Ning0612/esp32-paper-frame/docs/adr/0005-weather-worker-and-status-bar.md

# ADR-0005：WeatherWorker HTTPS 契約與狀態列渲染基線

- Status: accepted
- Date: 2026-07-31
- Supersedes: none

## Context

`docs/archive/IMPLEMENTATION_PLAN.md` 的 Gate G7（"OpenWeatherMap endpoint/version、
TLS trust、cache schema 與 rate limit"）與狀態列 renderer 的字型/圖示來源
必須在 Phase 6 開工前固定，不能沿用草案「建議」直接實作。掃描確認：全專案
目前沒有任何 `esp_http_client`/`esp_tls`/`esp_crt_bundle` 用例、SNTP/mDNS
完全未整合、狀態列目前是整片填白（無文字/圖示繪製能力）。本 ADR 記錄
WeatherWorker（`pf_weather_worker` component）與狀態列渲染（`pf_display`
的 bitmap font/icon 原語）實作前必須固定的決策。

## Decision

### G7：OpenWeatherMap endpoint / TLS trust / cache schema / rate limit

- **Endpoint**：`GET https://api.openweathermap.org/data/2.5/weather`，
  查詢參數 `lat`、`lon`（由 `WeatherSettings.latitude_e6`/`longitude_e6`
  換算為十進位度）、`appid`、`units`、`lang`。對應既有
  `pf_weather::parse_current_weather` 已假設的回應欄位
  （`main.temp`、`main.humidity`、`weather[0].id/description/icon`、
  `dt`、`name`），不需要改動 parser 契約。
- **TLS trust**：使用 `esp_crt_bundle_attach`（`esp_http_client_config_t`
  的 `crt_bundle_attach` 欄位）。`sdkconfig.paperframe-s3` 已啟用
  `CONFIG_MBEDTLS_CERTIFICATE_BUNDLE=y` 與
  `CONFIG_MBEDTLS_CERTIFICATE_BUNDLE_DEFAULT_FULL=y`，不釘選、不內嵌自訂
  憑證。TLS 憑證有效期驗證需要正確的系統時間，因此 WeatherWorker 在首次
  請求前必須等待 `RuntimeSnapshot.time_sync == synced`（見下方 SNTP 決策）。
- **Cache schema**：直接複用既有 `pf_weather::Observation`/`Cache`
  （`components/pf_weather/include/pf_weather/weather.hpp`），不重新定義。
  `RuntimeSnapshot` 內嵌一份精簡欄位（`weather_observation`、
  `weather_units`、`weather_has_observation`、
  `weather_last_success_epoch_s`、`weather_consecutive_failures`、
  `weather_last_failure`），值語意複製，不使用指標，維持
  `RuntimeSnapshot` 的 trivially-copyable 契約。
- **Rate limit / 更新頻率**（**已被 [ADR-0014](0014-weather-panel-refresh-cadence-and-map-picker.md) 取代**）：
  改採 `WeatherSettings.update_interval_minutes`
  （使用者可設 10–1440 分鐘）取代 `pf_weather::kUpdateIntervalMs` 目前寫死
  的 10 分鐘；`pf_weather::record_success` 擴充一個 `interval_ms` 參數，
  預設值等於原常數以維持既有呼叫端相容。OpenWeatherMap 免費額度為
  60 requests/min，在 10–1440 分鐘區間內完全無虞，不需要額外的用戶端節流。

### SNTP：最小可用的時間同步

- NetworkServiceTask（既有 `pf_network::NetworkService`，
  `docs/archive/IMPLEMENTATION_PLAN.md` 第 60 行已將其列為 SNTP owner）在 STA
  首次取得 IP 後啟動 SNTP：`esp_netif_sntp_init` +
  `ESP_NETIF_SNTP_DEFAULT_CONFIG`，伺服器名稱來自
  `WeatherSettings.ntp_server`（預設 `pool.ntp.org`），透過
  `sntp_set_time_sync_notification_cb` 註冊回呼。
- 新增 `pf_network::TimeSyncState { unsynced, syncing, synced }`
  （純邏輯，`components/pf_network/include/pf_network/time_sync_state.hpp`）。
  刻意不設 `failed` 狀態：ESP-IDF 的 SNTP 客戶端沒有終止性失敗的概念，
  啟動後會持續在背景重試，沒有事件可以驅動這樣的狀態。
- `RuntimeSnapshot` 鏡射一份同名 `TimeSyncState`（避免 `pf_runtime`
  反向依賴 `pf_network`，沿用既有 `WifiState`/`InternetState` 的鏡射＋
  轉譯慣例），`RuntimeCoordinator::update_time_sync(...)` 是唯一寫入口。
- 本次只處理「STA 連上後啟動 SNTP、追蹤 synced 狀態」，不處理 AP/
  Recovery AP 模式下的時間行為，也不做未同步狀態的完整診斷分類；
  WeatherWorker 與狀態列渲染只需要一個布林等級的「時間是否可信」訊號。

### Internet 可達性訊號

- `NetworkStateMachine` 已定義 `internet_reachable`/`internet_unreachable`
  事件，但全專案沒有任何呼叫端觸發，導致 `internet` 狀態永遠停在
  `unknown`。WeatherWorker 是第一個會發出 HTTPS 請求的元件，因此由它
  透過 `NetworkService::report_internet_state(bool reachable)`
  （比照 `request_scan()` 的直接呼叫模式）回報：
  - `pf_weather::Cache::Failure::network`（DNS 解析、連線建立、TLS
    handshake 失敗）→ `unreachable`。
  - 其餘結果（成功、`api_key_invalid`、`http_error`、`parse_error`——
    皆代表已收到 HTTP 回應，代表連線本身是通的）→ `reachable`。
- 對應 `docs/archive/IMPLEMENTATION_PLAN.md` 第 203 行的既有原則：
  「DNS、weather 或 Internet 錯誤只改變 Internet 狀態，不進 AP」。

### 字型與圖示授權（**圖示部分已被 ADR-0013 取代**）

- 狀態列渲染（日期、星期、weather icon、temperature、stale 標記）採用
  **自製最小點陣字型**（僅涵蓋數字、`:`、`/`、`-`、`°`、`%`、星期縮寫
  所需的拉丁字母，本段落仍然有效）與 **9 組簡化天氣圖示分類**（對映
  OpenWeatherMap icon code 的天氣狀況群組）。天氣圖示原本的決策是「皆為
  本專案原創點陣資料，不引入任何第三方字型或圖示檔案，避免授權查證與
  再散布限制的負擔」——這個部分已被
  [ADR-0013](0013-weather-icon-bitmaps-from-third-party-ofl-source.md)
  取代：圖示改為轉檔自 `erikflowers/weather-icons`（OFL-1.1）的點陣圖，
  9 組分類本身不變。點陣字型（數字/日期）維持原創，不受影響。

## Consequences

- `pf_weather_worker` 是本專案第一個使用 `esp_http_client`/`esp-tls`/
  `mbedtls` 的 component；CMakeLists 需新增對應 `REQUIRES`。
- WeatherWorker 讀取設定一律呼叫 `pf_config::load_weather_settings()`
  直接讀 NVS，不與 `health_server.cpp` 內的 `server_access_config` 共用
  記憶體狀態，避免新增跨 component 耦合；使用者存檔後由
  `process_weather_config()` 呼叫 WeatherWorker 的
  `request_immediate_refresh()` 提前喚醒，不必等到下一個排程週期。
- 狀態列內容更新沿用既有整頁 refresh 節奏（不新增 `CommandKind`、不做
  局部刷新驅動）；天氣本身 10–1440 分鐘的更新頻率與既有 5–30 分鐘
  carousel refresh 週期已經匹配，此設計為刻意簡化，非遺漏
  （**更新頻率的排程來源本身已被 [ADR-0014](0014-weather-panel-refresh-cadence-and-map-picker.md)
  取代**：不再有獨立的使用者可調間隔，改為 carousel 每次面板刷新前
  觸發，但「沿用整頁 refresh 節奏、不做局部刷新」這個更上層的設計仍然
  成立）。
- 未來若要改變 endpoint、TLS 策略或字型/圖示來源，需要新的 superseding
  ADR，而不是直接修改程式碼繞過本決策。

## Verification

- `pio run` 與 `pio test -e native` 全綠是本 ADR 所涵蓋所有變更的最低
  驗證門檻；HTTPS/SNTP 的實際網路行為無法 host test，須在
  `docs/hardware/VALIDATION.md` 記錄實機驗證（API key invalid、
  DNS/TLS/timeout 各自診斷狀態、stale 顯示、未同步時間 fallback）。
- `esp_crt_bundle_attach` 驗證 `api.openweathermap.org` 憑證成功，是
  WeatherWorker 第一次成功抓取的前提條件，須在實機記錄。

## Update (2026-08)

反過度設計整併：`pf_weather_worker` component 已併入 `pf_weather`，
namespace 由 `pf_weather_worker` 改為 `pf_weather`（`WeatherWorker` 類別
本體與本 ADR 記錄的所有決策不變，純粹是元件邊界調整，不是 superseding
ADR 的範疇）。本文其餘內容提到的 `pf_weather_worker` 是撰寫當下的元件
名稱，保留作歷史紀錄。

## Update (2026-08-03)

狀態列版面依產品需求固定為：日期左側顯示
`YYYY-MM-DD-<英文星期縮寫>`（例如 `2026-08-03-Mon`），裝置 IPv4 位址置中。
環境感測器狀態為 `online` 且有有效 reading 時，OpenWeatherMap 天氣圖示與
室外溫度接在日期右側，最右側顯示室內溫度與溼度；感測器未啟用或沒有有效
reading 時，右側室內欄位改顯示天氣圖示與室外溫度。IP 由 `NetworkService` 發布至唯一的
`RuntimeSnapshot`，不由 renderer 直接查詢網路介面。480px 直向狀態列採
較小點陣字級以保留三區的獨立位置；`^` 是韌體內部的一位元組度數符號。

## Update (2026-08-21)

本段落取代前述「SNTP：最小可用的時間同步」一節裡「不處理未同步狀態的完整診斷分類」
之外的範圍限制：狀態列現在會換算成使用者設定的當地時間，不再固定顯示 UTC。

- `ConfigRecord.timezone`（`pf_config` schema，`char[kTimezoneCapacity]`）改變意義：
  schema v2 及以前存的是 IANA 區域名稱（如 `"Asia/Taipei"`），但全專案從未真的拿它換算
  時間；schema v3 起改存 UTC 偏移字串（`"+8"`、`"-5.5"`、`"+5.75"`），由
  `pf_config::parse_timezone_offset_minutes()` 解析成分鐘數，支援到 15 分鐘（0.25 小時）
  精度以涵蓋 Nepal（+5:45）、Chatham Islands（+12:45）等半/45 分鐘時區，範圍
  UTC-12〜UTC+14。這裡刻意不引入 IANA tzdata／DST 規則：ESP-IDF 沒有內建時區資料庫，
  韌體只承諾"使用者輸入的固定偏移"，不承諾"跟著地區行事曆自動調整 DST"。
- 這個偏移值透過 `RuntimeCoordinator::update_timezone_offset()` 鏡射進
  `RuntimeSnapshot.timezone_offset_minutes`（比照既有 `time_sync`/`internet` 的鏡射慣例）；
  `build_status_bar_content()`（`src/app_main.cpp`）在 `gmtime_r()` 之前把 SNTP 取得的
  UTC epoch 加上這個偏移，換算出的日期／星期即為當地時間。除了狀態列這一處，其餘
  epoch 用途（快取新鮮度、OTA 時間戳記）仍刻意維持 UTC，避免時區偏移污染以「距今
  多少秒」為準的比較邏輯。
- WebUI「天氣與時間」頁新增一個獨立的「時區」面板／表單（`data/web/index.html`
  `#timezone-form`），透過既有 `/api/v1/config`（`CarouselConfigForm` 新增可選的
  `timezone` 欄位）保存，與 `refresh_minutes`/`random` 共用同一筆 `ConfigRecord`，
  但各自獨立可省略。
- Schema 由 v2 bump 到 v3；pre-v3 記錄遷移時，`timezone` 一律重設為新預設值 `"+8"`
  （不嘗試把舊的 IANA 名稱轉換成偏移——這欄位過去從未生效，沒有需要保留的使用者狀態）。

## Update (2026-08-04)

本段取代 2026-08-03 段落中的狀態列群組定位方式。依產品 UI 調整，狀態列仍
固定為 40px 高，但天氣圖示改為 36×36px，垂直位置
固定保留上下各 2px。橫向點陣文字放大為 4 倍，直向優先使用 3 倍；若直向
同時顯示最長的日期、IPv4、天氣與室內資訊而寬度不足，才退回 2 倍，讓文字
在同一個 40px 高度內保持可讀。日期、天氣（圖示／室外溫度）、IP、
室內溫度／溼度現在以內容寬度排列，存在的群組之間使用相同的可用空白；
缺少天氣或室內 reading 時只移除對應群組，不改變其他資訊的等距分配。

## Update (2026-09-03)

本段取代 2026-08-03 段落中「環境感測器狀態為 `online` 且有有效 reading
時才顯示室內溫濕度」的條件。使用者回報：全刷間隔（預設 30 分鐘）遠長於
原本的過期門檻（5 分鐘），單次 DHT22 讀取失敗、進入重試退避時，剛好被
全刷抓到就會讓室內欄位整個消失一輪。修正比照既有的 `weather_available`／
`weather_stale` 模式，新增 `indoor_stale`：室內欄位現在只要「已有成功讀值
（`has_reading`）且 `SensorStatus` 為 `online` **或** `stale`」就顯示
（過期門檻同時放寬到 3600 秒，比照 `pf_weather` 的門檻），過期時在數值
後方加一個紅色 `*` 標記；其餘狀態（`disabled`／`not_detected`／
`probing`／`error`，以及尚未成功讀過任何一次的情況）一律整個隱藏
（判斷邏輯集中在 `pf_sensors::environment_display_decision()`，見
`components/pf_sensors/include/pf_sensors/environment_sensor.hpp`）。
`kEnvironmentUpdateIntervalMs` 同時由 60 秒調整為 120 秒，是獨立的
DHT22 自熱誤差考量，與本次過期顯示的修正無直接關聯。
