Ning0612/esp32-paper-frame/partitions/paperframe-dev.csv

# Name | Type | SubType | Offset | Size | Flags
nvs | data | nvs | 0x9000 | 0x4000
otadata | data | ota | 0xd000 | 0x2000
phy_init | data | phy | 0xf000 | 0x1000
ota_0 | app | ota_0 | 0x10000 | 0x280000
ota_1 | app | ota_1 | 0x290000 | 0x280000
webfs | data | spiffs | 0x510000 | 0x100000
coredump | data | coredump | 0x610000 | 0x020000
imagefs | data | spiffs | 0x630000 | 0x9d0000
