Ning0612/esp32-paper-frame/docs/archive/README.md

# 歷史文件封存

本目錄保存已完成階段的需求快照與開發計畫，供追溯背景、決策來源與演進脈絡使用；其中內容不再作為現行產品規格、進度或驗收狀態的唯一依據。

## 文件

- [`Guild.md`](Guild.md)：ESP32-S3 電子紙圖片輪播專案的原始需求草案 v0.1。
- [`IMPLEMENTATION_PLAN.md`](IMPLEMENTATION_PLAN.md)：MVP 階段、驗收條件與原始 commit 邊界的詳細開發計畫。

## 現行文件入口

- [專案狀態](../PROJECT_STATUS.md)：目前已完成、待硬體驗證與待決策事項。
- [文件入口與分類](../README.md)：現行文件、操作文件、合約與歷史資料的分類。
- [架構決策](../adr/README.md)：已採用的架構決策與其追溯索引。

若封存文件與現行文件或程式行為不一致，以現行 contract、ADR、驗證紀錄與程式實作為準；新的行為變更請更新現行文件或新增 ADR，不要回頭改寫封存內容。
