Ning0612/esp32-paper-frame/components/pf_network/include/pf_network/ap_screen.hpp

#pragma once

#include <atomic>
#include <cstddef>
#include <cstdint>
#include <cstring>

#include "pf_config/secure_memory.hpp"

namespace pf_network {

inline constexpr std::size_t kApScreenSsidCapacity = 33U;
inline constexpr std::size_t kApScreenPasswordCapacity = 65U;
inline constexpr std::size_t kWifiQrCapacity = 160U;
inline constexpr std::size_t kWebQrCapacity = 48U;
inline constexpr std::uint64_t kApModeImageTimeoutMs =
    5U * 60U * 1000U;

inline bool should_hold_access_point_screen(
    const bool ap_mode,
    const bool has_displayable_image,
    const std::uint64_t now_ms,
    const std::uint64_t ap_mode_started_ms)
{
    if (!ap_mode) {
        return false;
    }
    if (!has_displayable_image) {
        return true;
    }
    return now_ms < ap_mode_started_ms ||
           now_ms - ap_mode_started_ms < kApModeImageTimeoutMs;
}

// app_main's main loop keeps a local mirror of "which AP session am I
// synced to" (ap_mode_active/ap_mode_ready/ap_mode_started_ms plus a
// session id copied from RuntimeSnapshot::ap_session_id). Two independent
// races made a plain "did wifi go true/false" transition check on that
// mirror unsafe (found by codex-cowork review, 2026-08-25):
//
// 1. The mirror is only refreshed once per loop tick, at the top. A
//    verdict computed from it later in the same tick (or carried into the
//    next) can be stale by the time it is actually used against the
//    submission mutex.
// 2. NetworkService can complete an entire `starting_ap -> provisioning`
//    cycle -- or even `provisioning -> starting_ap -> provisioning`
//    (prepare_ap() running again without ever leaving AP mode) -- between
//    two ticks that both observe `provisioning`, so a transition-based
//    diff never sees the intermediate state that would have triggered a
//    reset.
//
// classify_ap_mode_window() sidesteps both: `current_ap_session_id` is
// RuntimeCoordinator's monotonic counter (bumped on every fresh entry into
// `starting_ap`, including re-entries), so comparing it against the last
// session id the mirror was synced to detects a new/changed session
// regardless of how many intermediate ticks were missed.
enum class ApModeWindowAction : std::uint8_t {
    // Nothing to update -- current session, no readiness change, or
    // simply not in AP mode.
    unchanged,
    // Fresh entry into AP mode, or a same-mode restart (session id
    // changed while still ap_mode): resync ap_mode_active/ap_mode_ready/
    // ap_mode_started_ms/ap_mode_session_id from scratch.
    resync,
    // Same session, wifi just reached `provisioning` for the first time:
    // start the grace-window timer now.
    became_ready,
    // Left AP mode entirely: clear the mirror.
    ended,
};

inline ApModeWindowAction classify_ap_mode_window(
    const bool was_ap_mode_active,
    const bool was_ap_mode_ready,
    const std::uint32_t was_ap_session_id,
    const bool is_ap_mode,
    const bool is_ap_ready,
    const std::uint32_t current_ap_session_id)
{
    if (is_ap_mode && current_ap_session_id != was_ap_session_id) {
        return ApModeWindowAction::resync;
    }
    if (is_ap_mode && is_ap_ready && !was_ap_mode_ready) {
        return ApModeWindowAction::became_ready;
    }
    if (!is_ap_mode && was_ap_mode_active) {
        return ApModeWindowAction::ended;
    }
    return ApModeWindowAction::unchanged;
}

// The gate check behind try_lock_carousel_submission_gate() in
// src/app_main.cpp. `verdict_ap_session_id` is the session id the caller's
// (possibly stale) `ap_screen_owns_panel` verdict was computed against;
// `fresh_ap_session_id` is read fresh, inside the submission mutex, at
// gate time.
//
// The session-id mismatch check is deliberately scoped to
// `fresh_wifi_in_ap_mode` rather than applied unconditionally.
// RuntimeSnapshot::ap_session_id is never reset when AP mode ends -- it
// only counts entries into `starting_ap` -- while the caller resets its
// local mirror to 0 on exit (see ApModeWindowAction::ended). Comparing the
// two unconditionally would deny every submission for the rest of the
// device's uptime after the first AP session ever ends, since a
// permanently-0 local id could never again equal the snapshot's
// permanently-nonzero one (found by codex-cowork review, round 2,
// 2026-08-25). Once AP mode has genuinely ended, `ap_screen_owns_panel`
// itself already answers "false" correctly on its own -- the session id
// only needs to matter while AP mode might still legitimately own the
// panel.
inline bool submission_gate_denies_for_ap_session(
    const bool ap_screen_owns_panel,
    const bool fresh_wifi_in_ap_mode,
    const std::uint32_t fresh_ap_session_id,
    const std::uint32_t verdict_ap_session_id)
{
    return ap_screen_owns_panel ||
           (fresh_wifi_in_ap_mode &&
            fresh_ap_session_id != verdict_ap_session_id);
}

struct AccessPointScreenPayload {
    char ssid[kApScreenSsidCapacity]{};
    char password[kApScreenPasswordCapacity]{};
    char ip_address[16]{};
    char wifi_qr[kWifiQrCapacity]{};
    char web_qr[kWebQrCapacity]{};
    char device_suffix[5]{};
};

template <std::size_t Capacity>
inline bool copy_ap_screen_text(
    char (&destination)[Capacity],
    const char* const source)
{
    if (source == nullptr) {
        return false;
    }
    const std::size_t length = std::strlen(source);
    if (length >= Capacity) {
        return false;
    }
    std::memcpy(destination, source, length + 1U);
    return true;
}

inline bool append_qr_text(
    char* const destination,
    const std::size_t capacity,
    std::size_t& length,
    const char* const source,
    const bool escape_wifi)
{
    if (destination == nullptr || source == nullptr) {
        return false;
    }
    for (std::size_t index = 0U;
         source[index] != '\0';
         ++index) {
        const char value = source[index];
        const bool escaped =
            escape_wifi &&
            (value == '\\' || value == ';' ||
             value == ',' || value == ':' ||
             value == '"');
        if (length + (escaped ? 2U : 1U) >= capacity) {
            return false;
        }
        if (escaped) {
            destination[length++] = '\\';
        }
        destination[length++] = value;
    }
    destination[length] = '\0';
    return true;
}

inline bool build_access_point_screen_payload(
    const char* const ssid,
    const char* const password,
    const char* const device_suffix,
    AccessPointScreenPayload& destination)
{
    if (ssid == nullptr || password == nullptr ||
        device_suffix == nullptr ||
        std::strlen(device_suffix) != 4U ||
        std::strlen(password) < 8U) {
        return false;
    }

    AccessPointScreenPayload candidate{};
    const pf_config::SecureZeroGuard candidate_guard(candidate);
    if (!copy_ap_screen_text(candidate.ssid, ssid) ||
        !copy_ap_screen_text(candidate.password, password) ||
        !copy_ap_screen_text(
            candidate.ip_address,
            "192.168.4.1") ||
        !copy_ap_screen_text(
            candidate.web_qr,
            "http://192.168.4.1/") ||
        !copy_ap_screen_text(
            candidate.device_suffix,
            device_suffix)) {
        return false;
    }

    std::size_t length = 0U;
    if (!append_qr_text(
            candidate.wifi_qr,
            sizeof(candidate.wifi_qr),
            length,
            "WIFI:T:WPA;S:",
            false) ||
        !append_qr_text(
            candidate.wifi_qr,
            sizeof(candidate.wifi_qr),
            length,
            ssid,
            true) ||
        !append_qr_text(
            candidate.wifi_qr,
            sizeof(candidate.wifi_qr),
            length,
            ";P:",
            false) ||
        !append_qr_text(
            candidate.wifi_qr,
            sizeof(candidate.wifi_qr),
            length,
            password,
            true) ||
        !append_qr_text(
            candidate.wifi_qr,
            sizeof(candidate.wifi_qr),
            length,
            ";;",
            false)) {
        return false;
    }
    destination = candidate;
    return true;
}

inline bool same_access_point_screen_payload(
    const AccessPointScreenPayload& left,
    const AccessPointScreenPayload& right)
{
    return std::memcmp(&left, &right, sizeof(left)) == 0;
}

bool render_access_point_screen(
    std::uint8_t* frame,
    std::size_t length,
    const AccessPointScreenPayload& payload);

// Tracks whether the AP instruction screen is what the panel is currently
// showing, so an unchanged payload can skip a ~31 s refresh.
//
// The skip is only sound while the claim is true. Holding the payload
// without tracking that -- which is what the presenter did until
// 2026-08-23 -- means the second AP session in a boot skips its refresh:
// the password, and so the payload, is unchanged since the first session,
// but the carousel has owned the panel in between. The radio then comes up
// with an image on the panel and the user cannot read the SSID, password
// or QR code, which is exactly when they need them.
//
// A named type rather than two loose fields, so `invalidate()` is a call
// site that can be found and tested instead of an assignment that is easy
// to forget.
// Two tasks touch this, so each field has exactly one writer.
// `payload`/`displayed` belong to the task that presents the AP
// screen; `superseded` is set by whichever task owns the panel
// afterwards. They share no lock on purpose: the presenter holds its
// submission mutex across a full ~31 s refresh, so making the panel
// owner wait for it would stall the carousel loop for half a minute.
//
// The residual race is deliberately biased safe. If an AP frame lands
// and an older carousel result is consumed just after, the cache is
// dropped while the AP screen really is on the panel -- costing one
// unnecessary refresh next session. The opposite error, claiming the
// panel while something else is on it, is the one that strands a user
// without their credentials, and that cannot happen: only the
// presenter sets the claim, and only after its own refresh.
struct AccessPointScreenCache {
    AccessPointScreenPayload payload{};
    bool displayed = false;
    std::atomic<bool> superseded{false};

    // True only when this exact payload is believed to be on the panel.
    bool shows(const AccessPointScreenPayload& candidate) const
    {
        return displayed &&
               !superseded.load(std::memory_order_acquire) &&
               same_access_point_screen_payload(payload, candidate);
    }

    void mark_displayed(const AccessPointScreenPayload& shown)
    {
        payload = shown;
        displayed = true;
        superseded.store(false, std::memory_order_release);
    }

    // Call whenever any other frame reaches the panel.
    void mark_superseded()
    {
        superseded.store(true, std::memory_order_release);
    }
};

}  // namespace pf_network
